spitzlbergerj/CO2-Messgeraet-ESP8266-MH-Z19B/img/github-CO2-Sensor-Gehäuse-real2.png

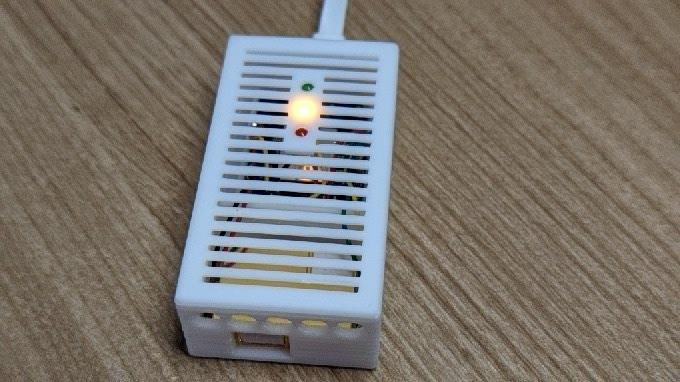
img/github-CO2-Sensor-Gehäuse-real2.png
