spitzlbergerj/CO2-Messgeraet-ESP8266-MH-Z19B/img/github-CO2-Sensor-Gehäuse-Unterteil.png

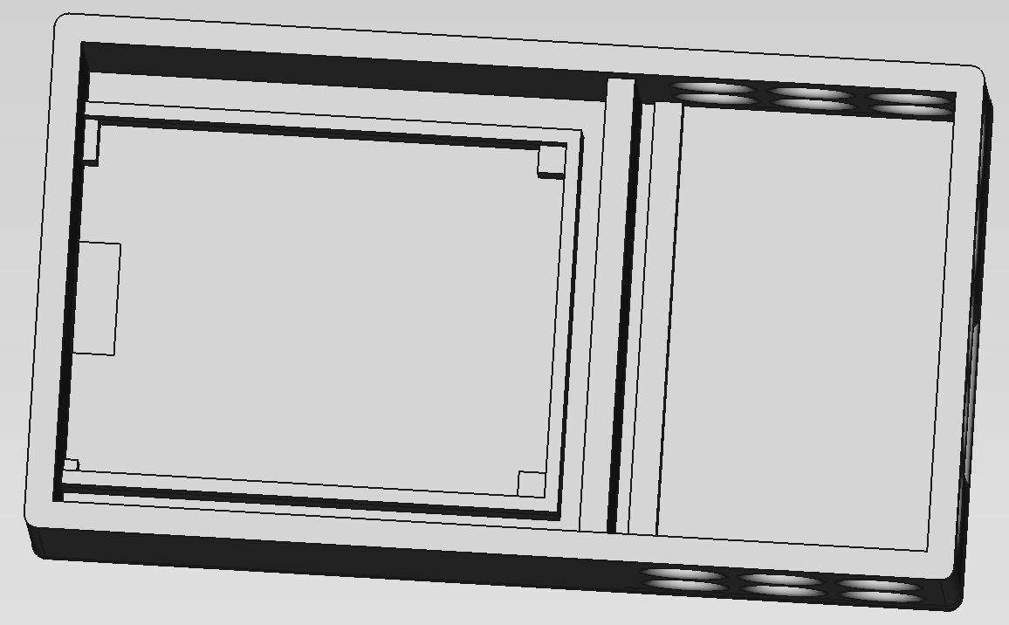
img/github-CO2-Sensor-Gehäuse-Unterteil.png
